zlkent/jcalendar/include/ota.h

#define HTTP_UE_TOO_LESS_SPACE              (-100)
#define HTTP_UE_SERVER_NOT_REPORT_SIZE      (-101)
#define HTTP_UE_SERVER_FILE_NOT_FOUND       (-102)
#define HTTP_UE_SERVER_FORBIDDEN            (-103)
#define HTTP_UE_SERVER_WRONG_HTTP_CODE      (-104)
#define HTTP_UE_SERVER_FAULTY_MD5           (-105)
#define HTTP_UE_BIN_VERIFY_HEADER_FAILED    (-106)
#define HTTP_UE_BIN_FOR_WRONG_FLASH         (-107)
#define HTTP_UE_NO_PARTITION                (-108)

void ota_update();
